ssingh-tamu/ECEN404-2026SP-TheOnlyWGT/Data/1V_1Hz_Square.png

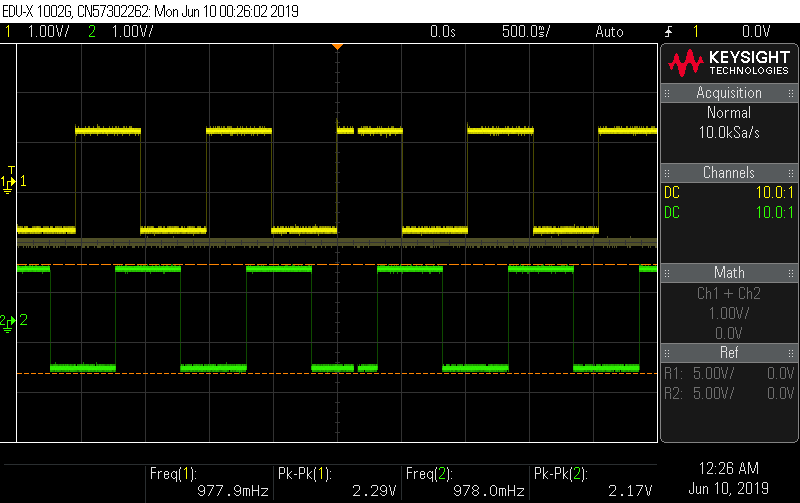
Data/1V_1Hz_Square.png
