ssingh-tamu/ECEN404-2026SP-TheOnlyWGT/Data/2V_1Hz_Sine.png

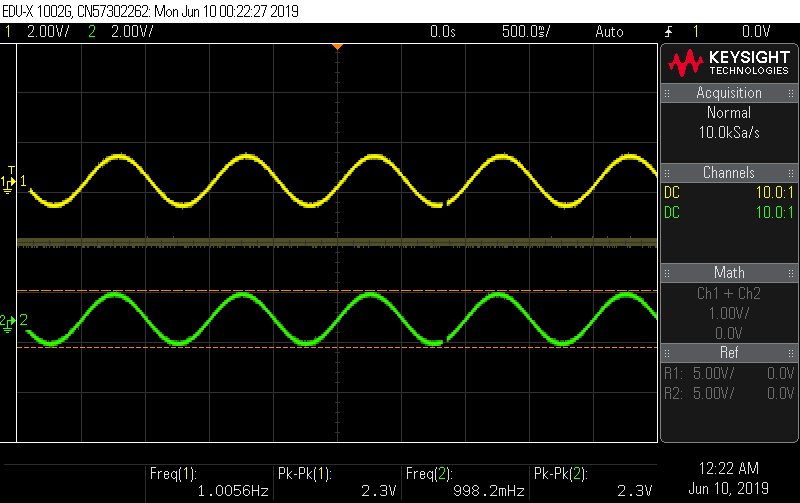
Data/2V_1Hz_Sine.png
