ssingh-tamu/ECEN404-2026SP-TheOnlyWGT/Data/2V_10kHz_Arbitrary.png

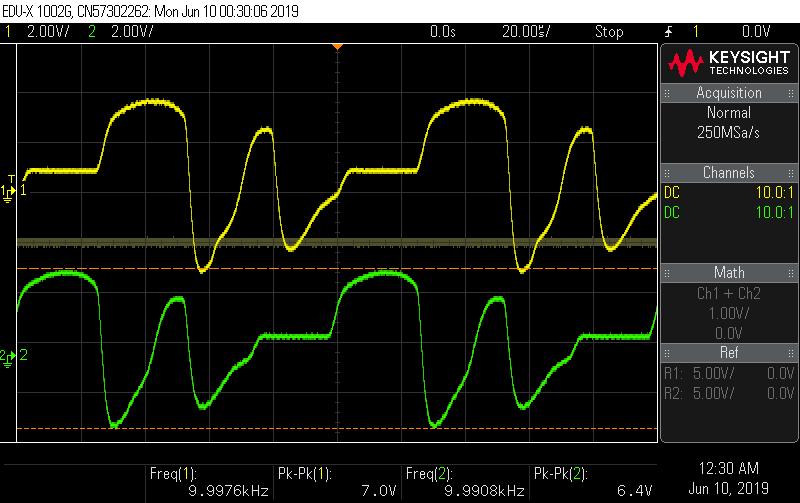
Data/2V_10kHz_Arbitrary.png
