ssingh-tamu/ECEN404-2026SP-TheOnlyWGT/Data/5V_100kHz_Sine.png

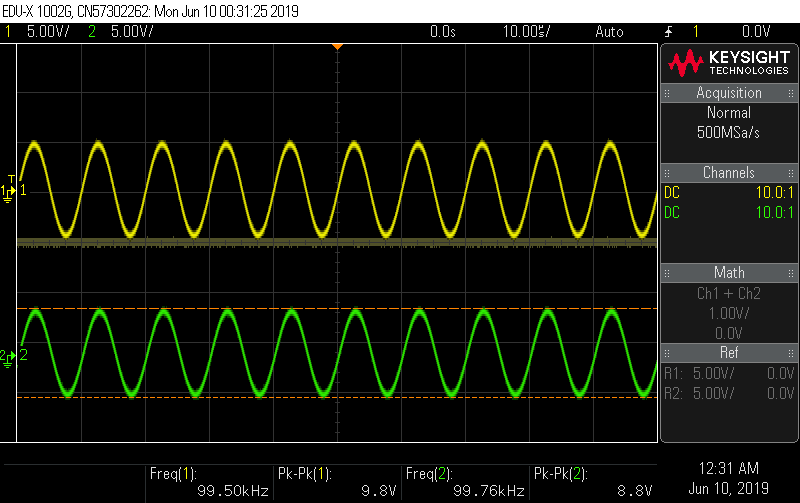
Data/5V_100kHz_Sine.png
