ssingh-tamu/ECEN404-2026SP-TheOnlyWGT/IMG_3190.PNG

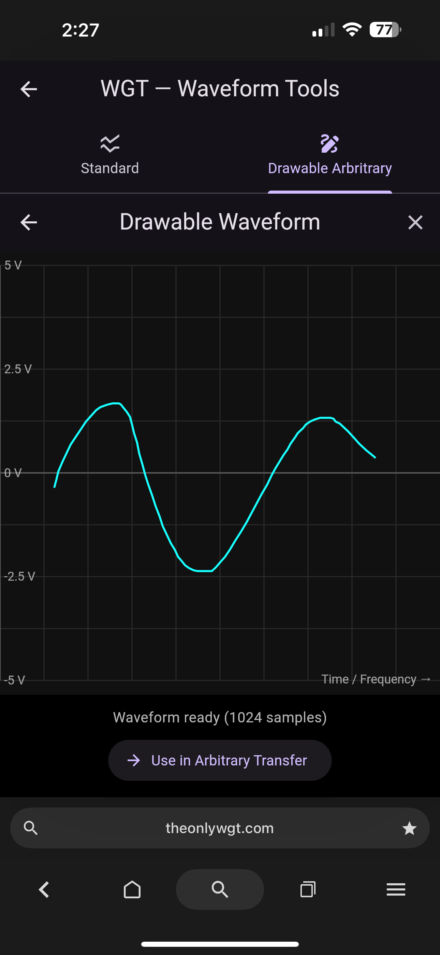
IMG_3190.PNG
