ssingh-tamu/ECEN404-2026SP-TheOnlyWGT/IMG_3191.PNG

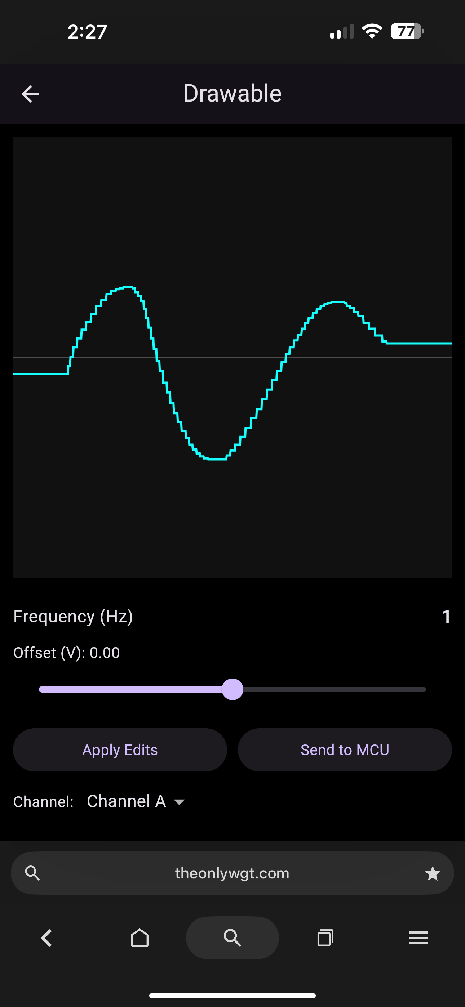
IMG_3191.PNG
