ssingh-tamu/ECEN404-2026SP-TheOnlyWGT/IMG_4054.jpg

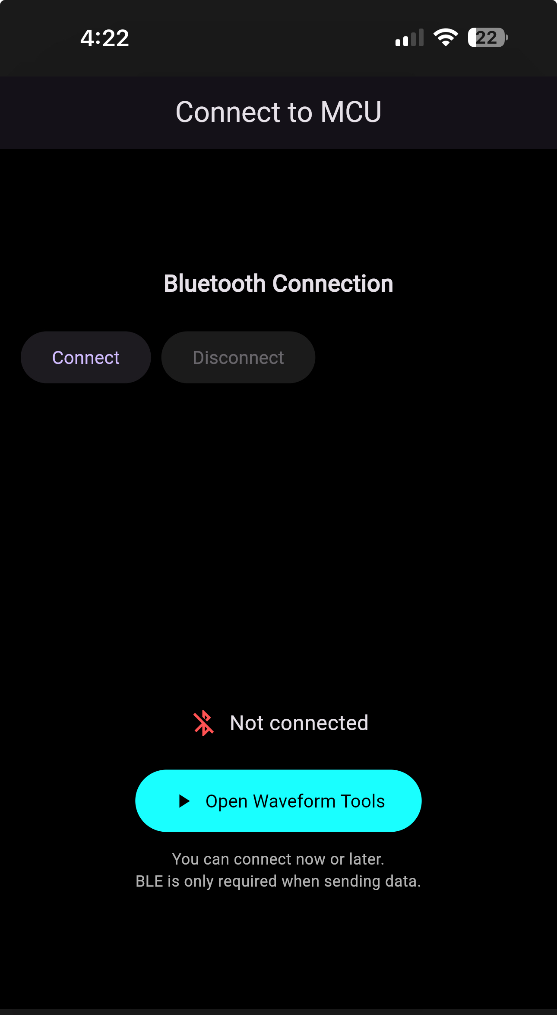
IMG_4054.jpg
