ssingh-tamu/ECEN404-2026SP-TheOnlyWGT/IMG_4055.PNG

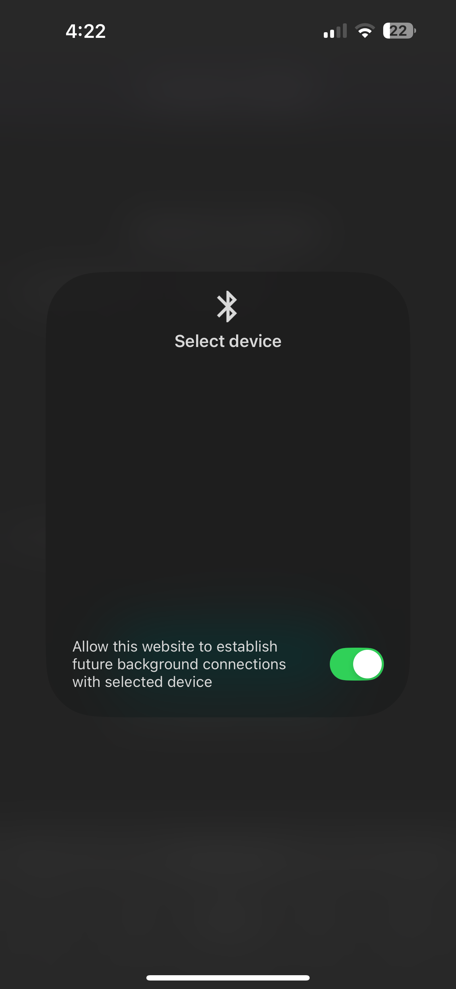
IMG_4055.PNG
