ssingh-tamu/ECEN404-2026SP-TheOnlyWGT/IMG_4056.jpg

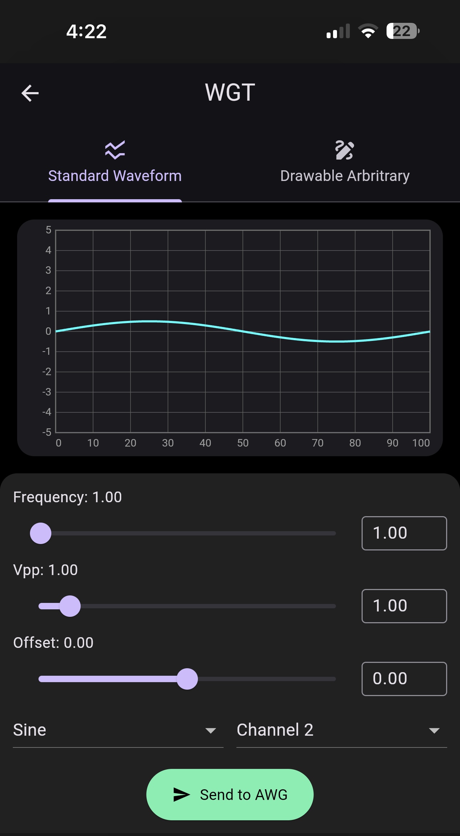
IMG_4056.jpg
