ssingh-tamu/ECEN404-2026SP-TheOnlyWGT/IMG_4057.jpg

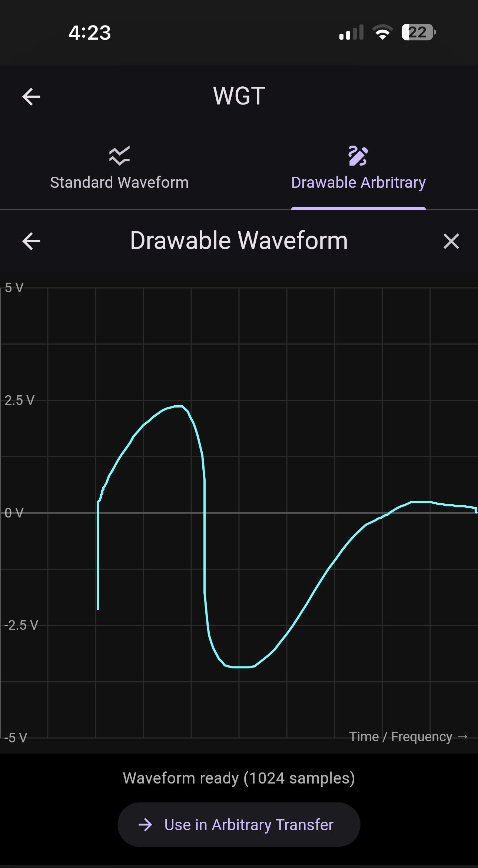
IMG_4057.jpg
