ssingh-tamu/ECEN404-2026SP-TheOnlyWGT/IMG_4058.jpg

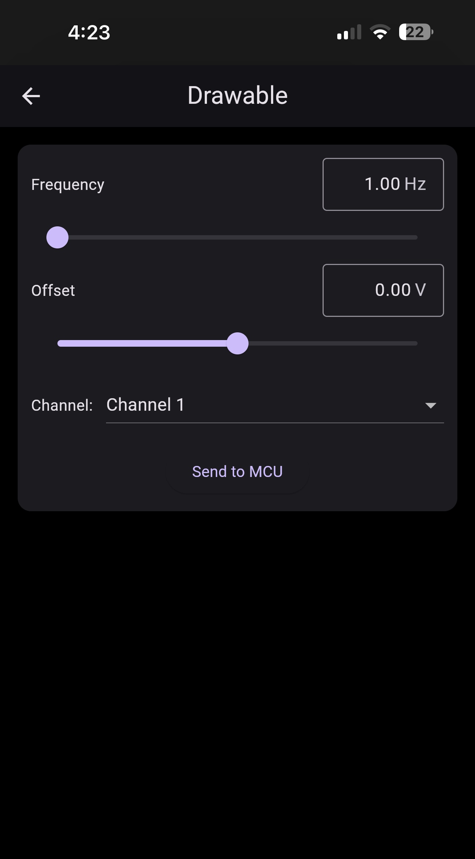
IMG_4058.jpg
